coronensis/cativity/v1/hardware/cativity.kicad_sch

## KiCad design v1/hardware/cativity.kicad_sch (2025-12-14)

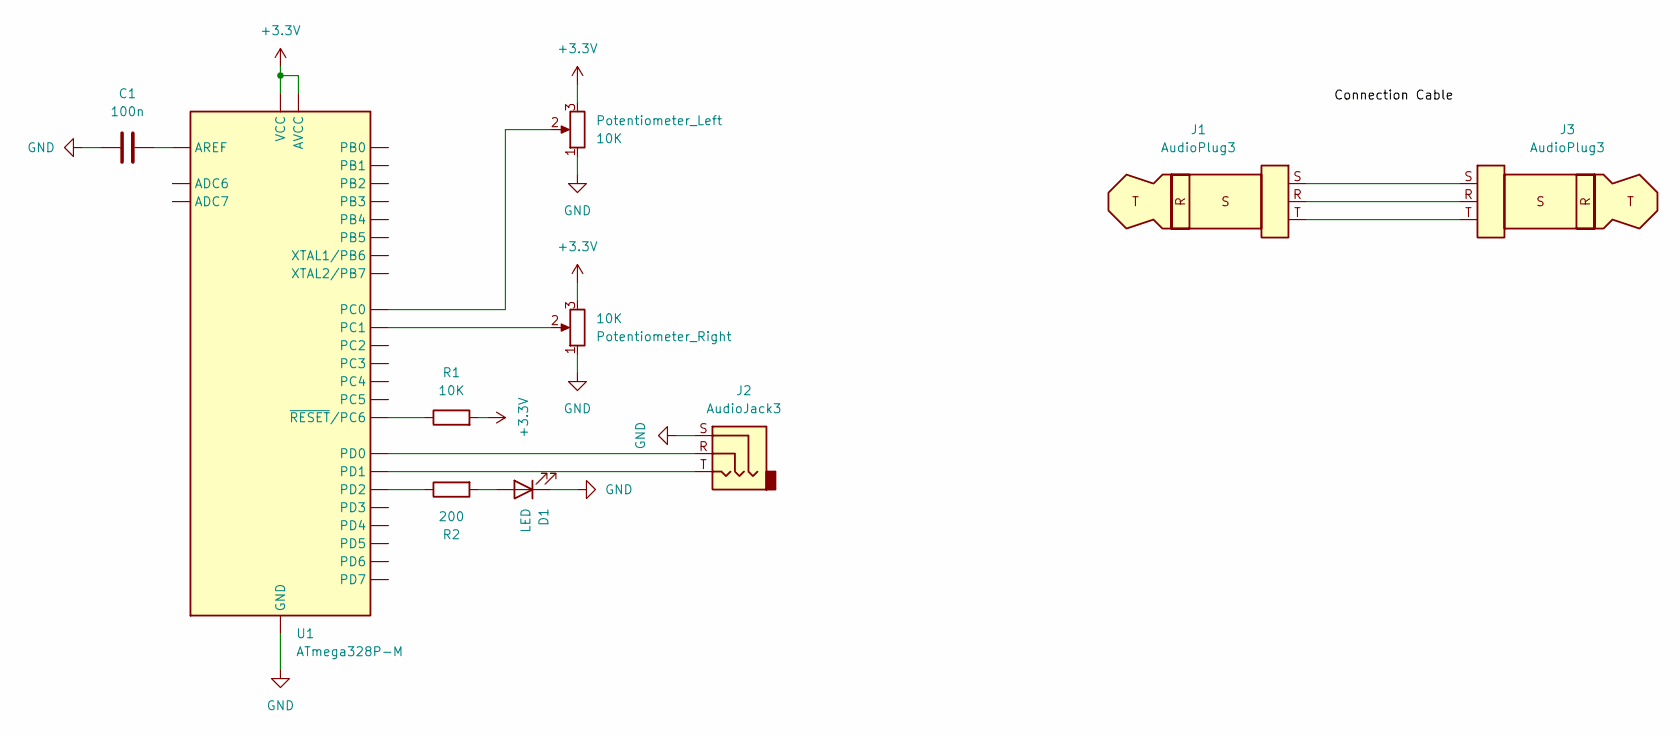
[picture p8: schematic cativity.kicad_sch]

Parts:
C1: 100n
D1: LED
J1, J3: AudioPlug3
J2: AudioJack3
Potentiometer_Left: 10K
Potentiometer_Right: 10K
R1: 10K
R2: 200
U1: ATmega328P-M; QFN-32-1EP_5x5mm_P0.5mm_EP3.1x3.1mm

Connections:
+3.3V: Potentiometer_Left.3, Potentiometer_Right.3, R1.2, U1.4 (VCC), U1.6 (VCC), U1.18 (AVCC)
GND: C1.2, D1.1 (K), J2.S, Potentiometer_Left.1, Potentiometer_Right.1, U1.3 (GND), U1.5 (GND), U1.21 (GND), U1.33 (GND)
unnamed: C1.1, U1.20 (AREF)
unnamed: D1.2 (A), R2.2
unnamed: J1.R, J3.R
unnamed: J1.S, J3.S
unnamed: J1.T, J3.T
unnamed: J2.R, U1.30 (PD0)
unnamed: J2.T, U1.31 (PD1)
unnamed: Potentiometer_Left.2, U1.23 (PC0)
unnamed: Potentiometer_Right.2, U1.24 (PC1)
unnamed: R1.1, U1.29 (~RESET/PC6)
unnamed: R2.1, U1.32 (PD2)
